fariszuh/12s-EV-Battery-Management-System/Referensi Desain Sebelumnya/BMS Winconsing Racing/218e_battery_design_board_tkhiNwzb7J.pdf

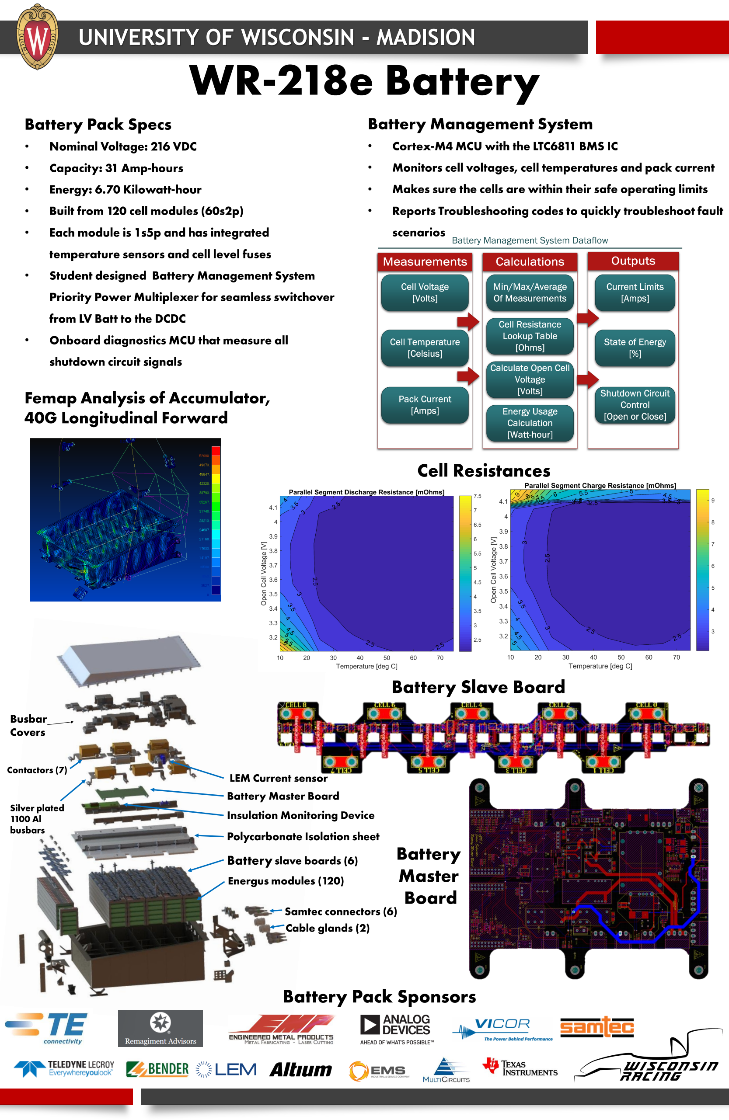
[picture p90: page 1]

UNIVERSITY OF WISCONSIN - MADISION

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
