fariszuh/12s-EV-Battery-Management-System/Referensi Desain Sebelumnya/BMS Orion/wiring overview.png

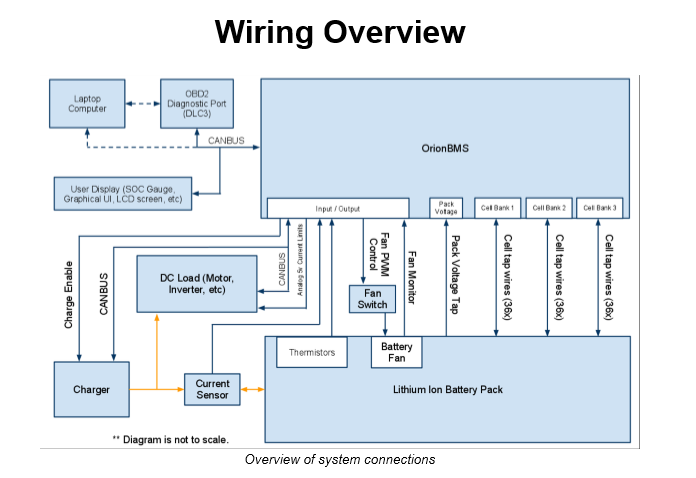
Referensi Desain Sebelumnya/BMS Orion/wiring overview.png
