fariszuh/12s-EV-Battery-Management-System/Adapter IC/Gerber/print.pdf

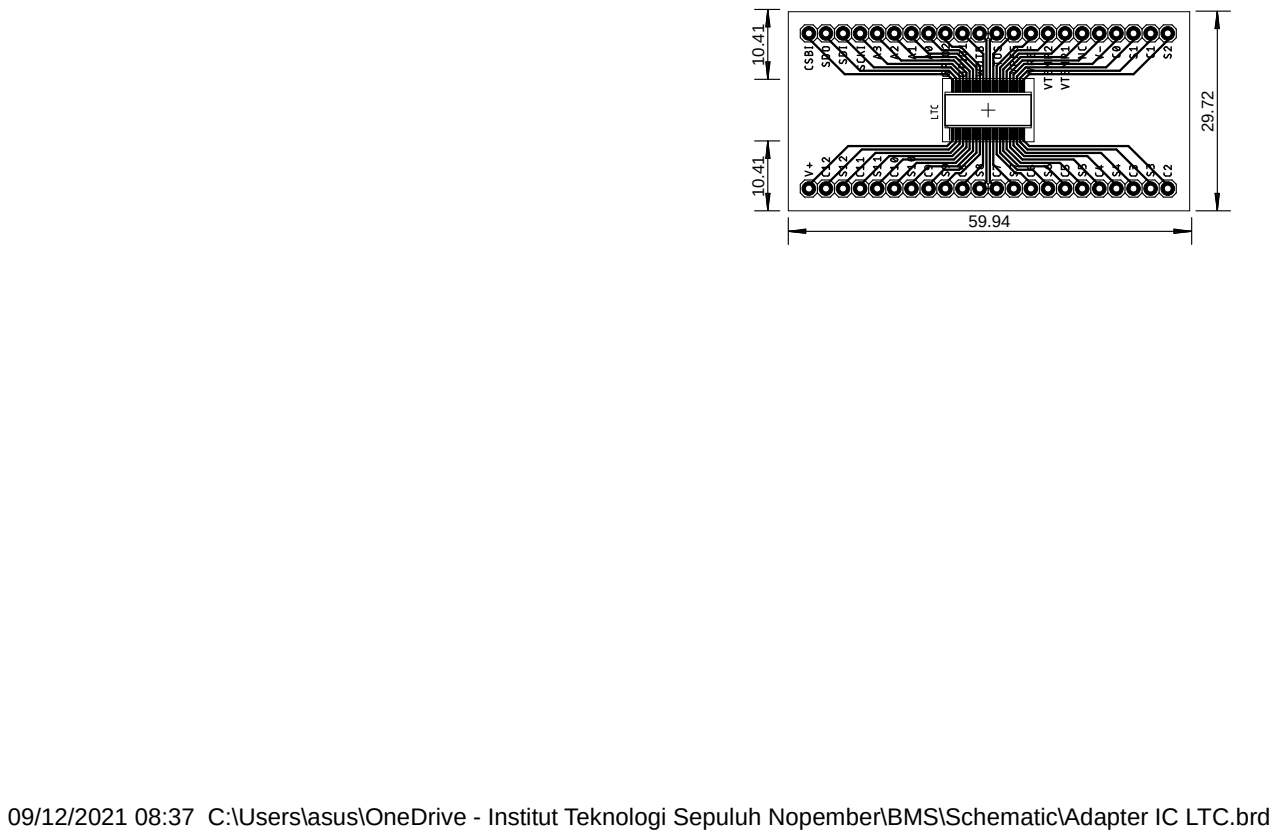
[picture p105: page 1]

09/12/2021 08:37 C:\Users\asus\OneDrive - Institut Teknologi Sepuluh Nopember\BMS\Schematic\Adapter IC LTC.brd

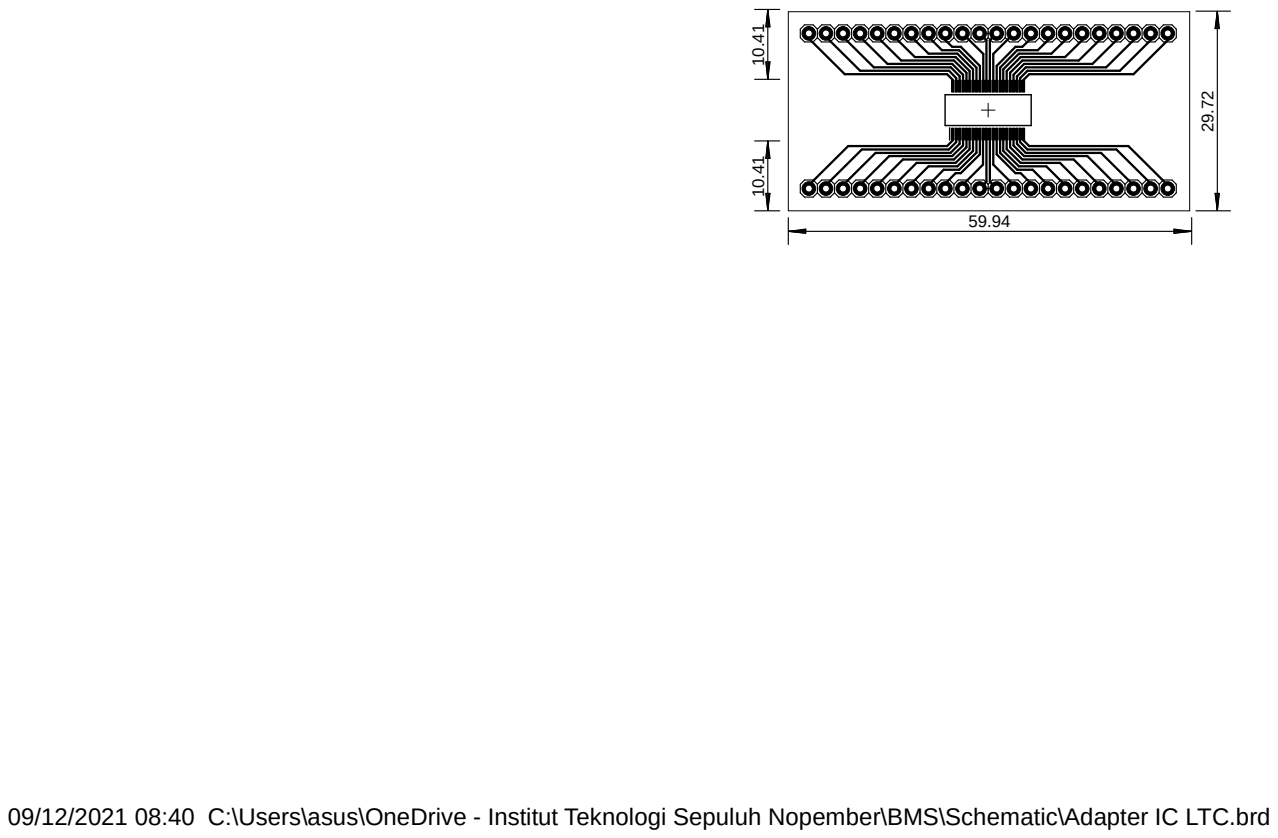
[picture p106: page 2]

09/12/2021 08:40 C:\Users\asus\OneDrive - Institut Teknologi Sepuluh Nopember\BMS\Schematic\Adapter IC LTC.brd
