fariszuh/12s-EV-Battery-Management-System/Referensi Desain Sebelumnya/BMS Winconsing Racing/battery_master_board_6TADGDZ8Km.pdf

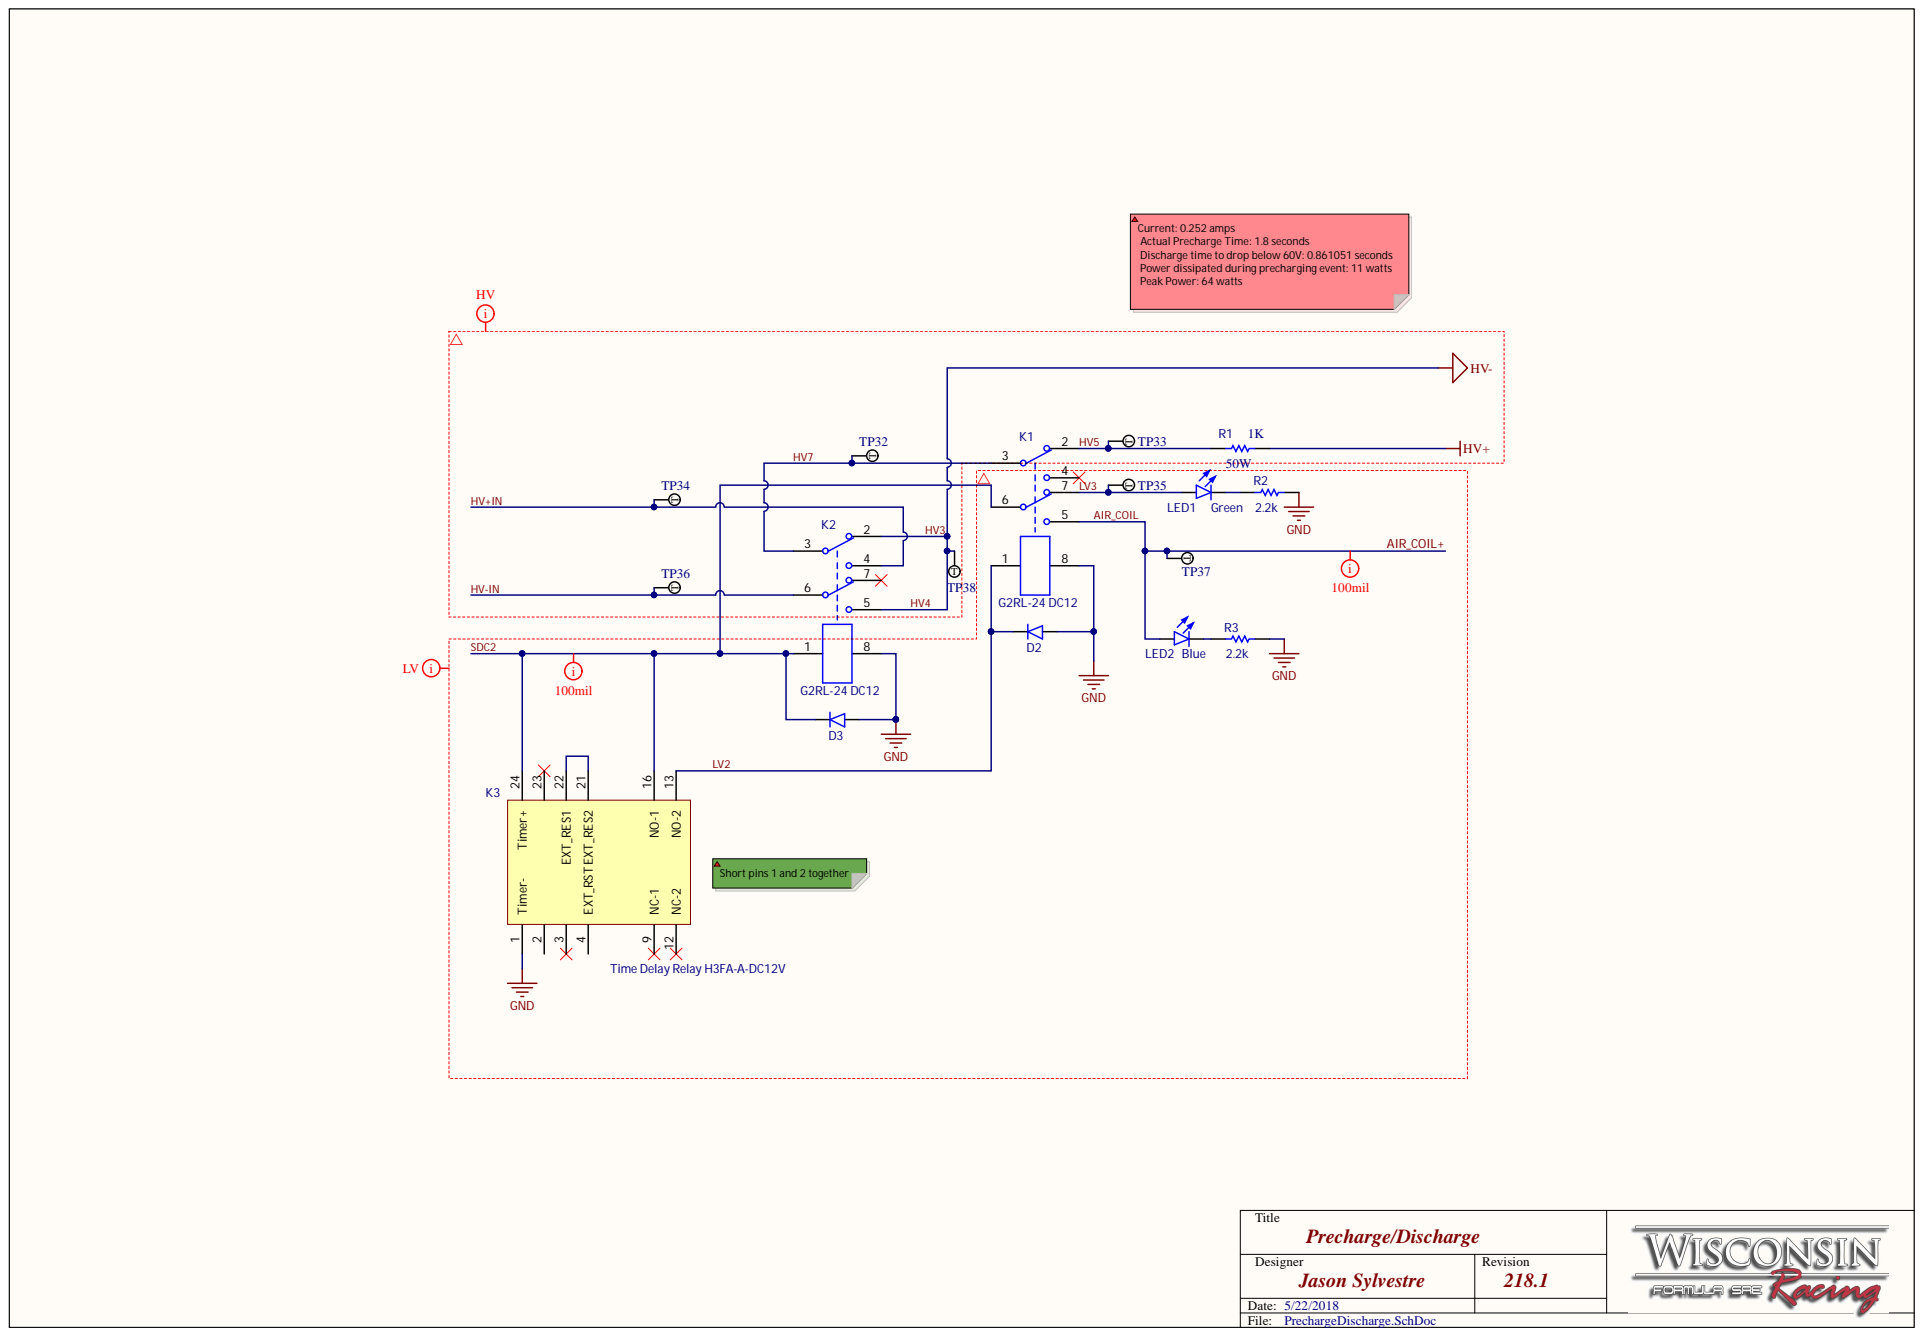
[picture p107: page 1]

Current: 0.252 amps
Actual Precharge Time: 1.8 seconds
Discharge time to drop below 60V: 0.861051 seconds
Power dissipated during precharging event: 11 watts
Peak Power: 64 watts

AIR_COIL

K2 2
3 4

Short pins 1 and 2 together

Title Precharge/Discharge

Designer Jason Sylvestre | Revision 218.1

Date:

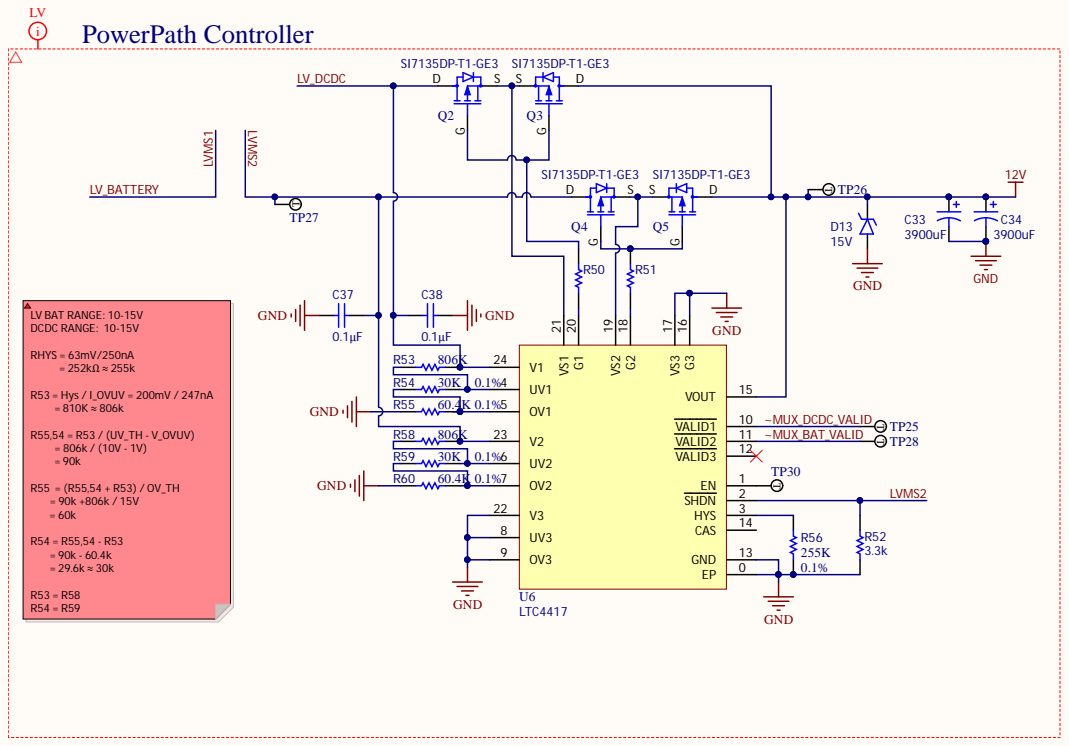
[picture p108: page 2]

R54 30K | 0.1% | UV1 4
R55 60.4K 0.1% | | OV1 5

R58 806K | | V2 23
R59 30K | 0.1% | UV2 6
R60 60.4K 0.1% | | OV2 7

Title Powerpath

Designer Jason Sylvestre | Revision 218.1

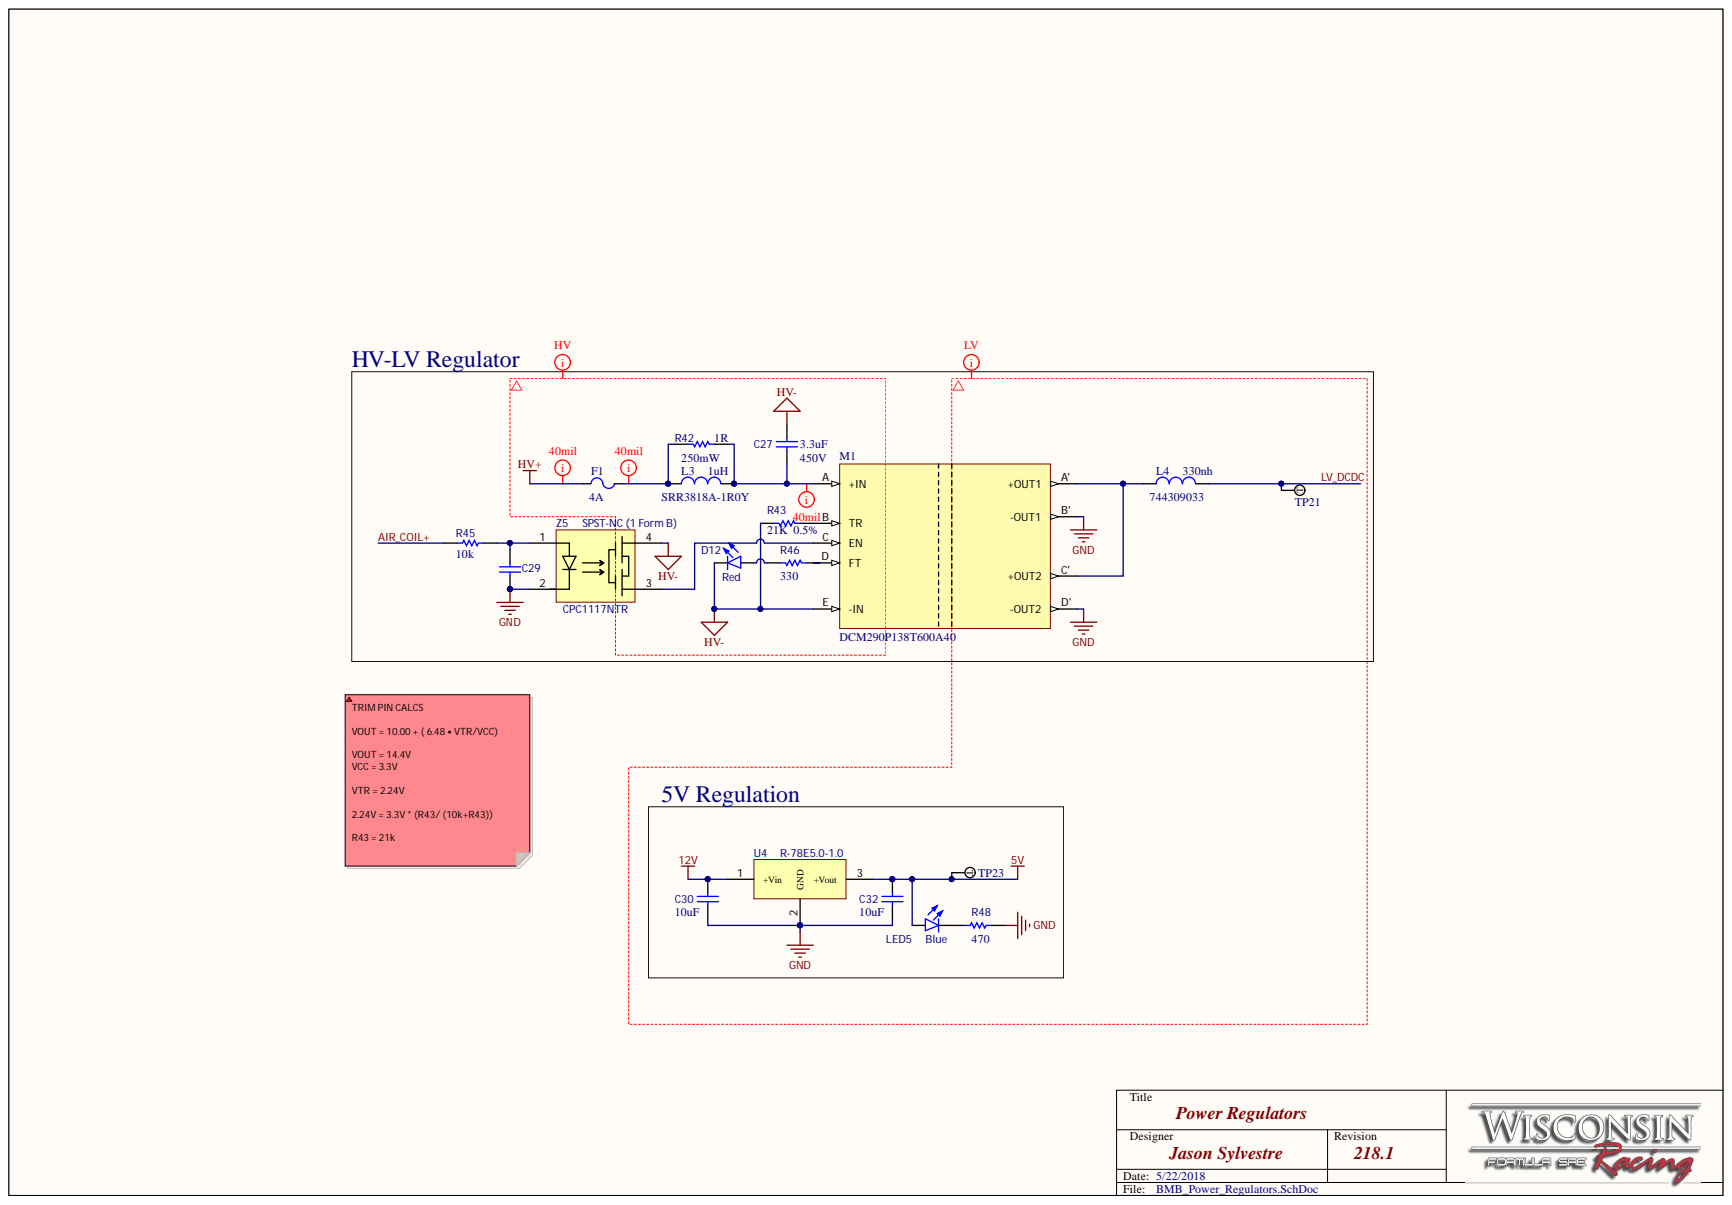
[picture p109: page 3]

Red | 330 | -IN E

Title Power Regulators

Designer Jason Sylvestre | Revision 218.1

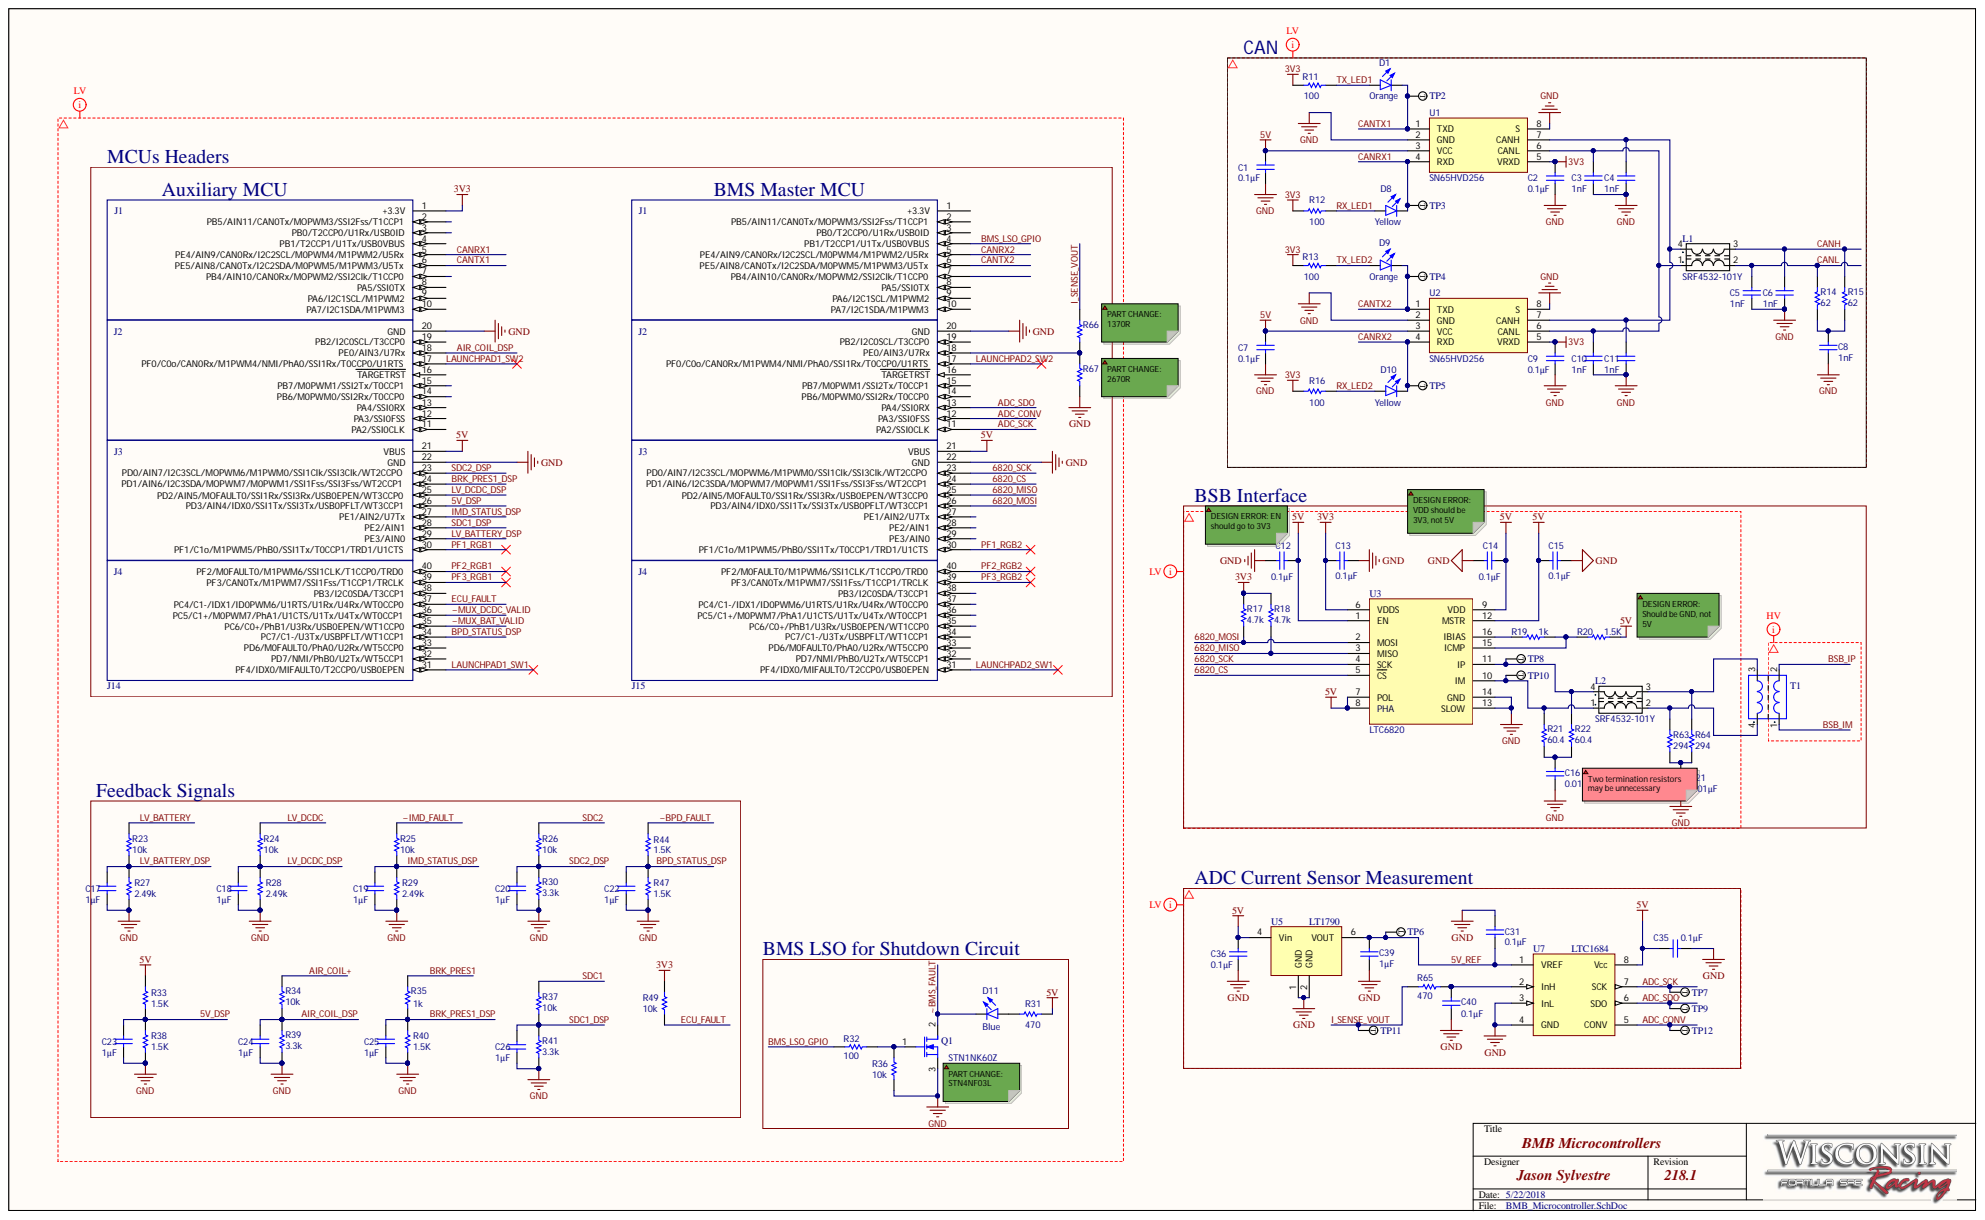
[picture p110: page 4]

ADC Current Sensor Measurement

BMS LSO for Shutdown Circuit

Title BMB Microcontrollers

Designer Jason Sylvestre | Revision 218.1

Date: 5/22/2018

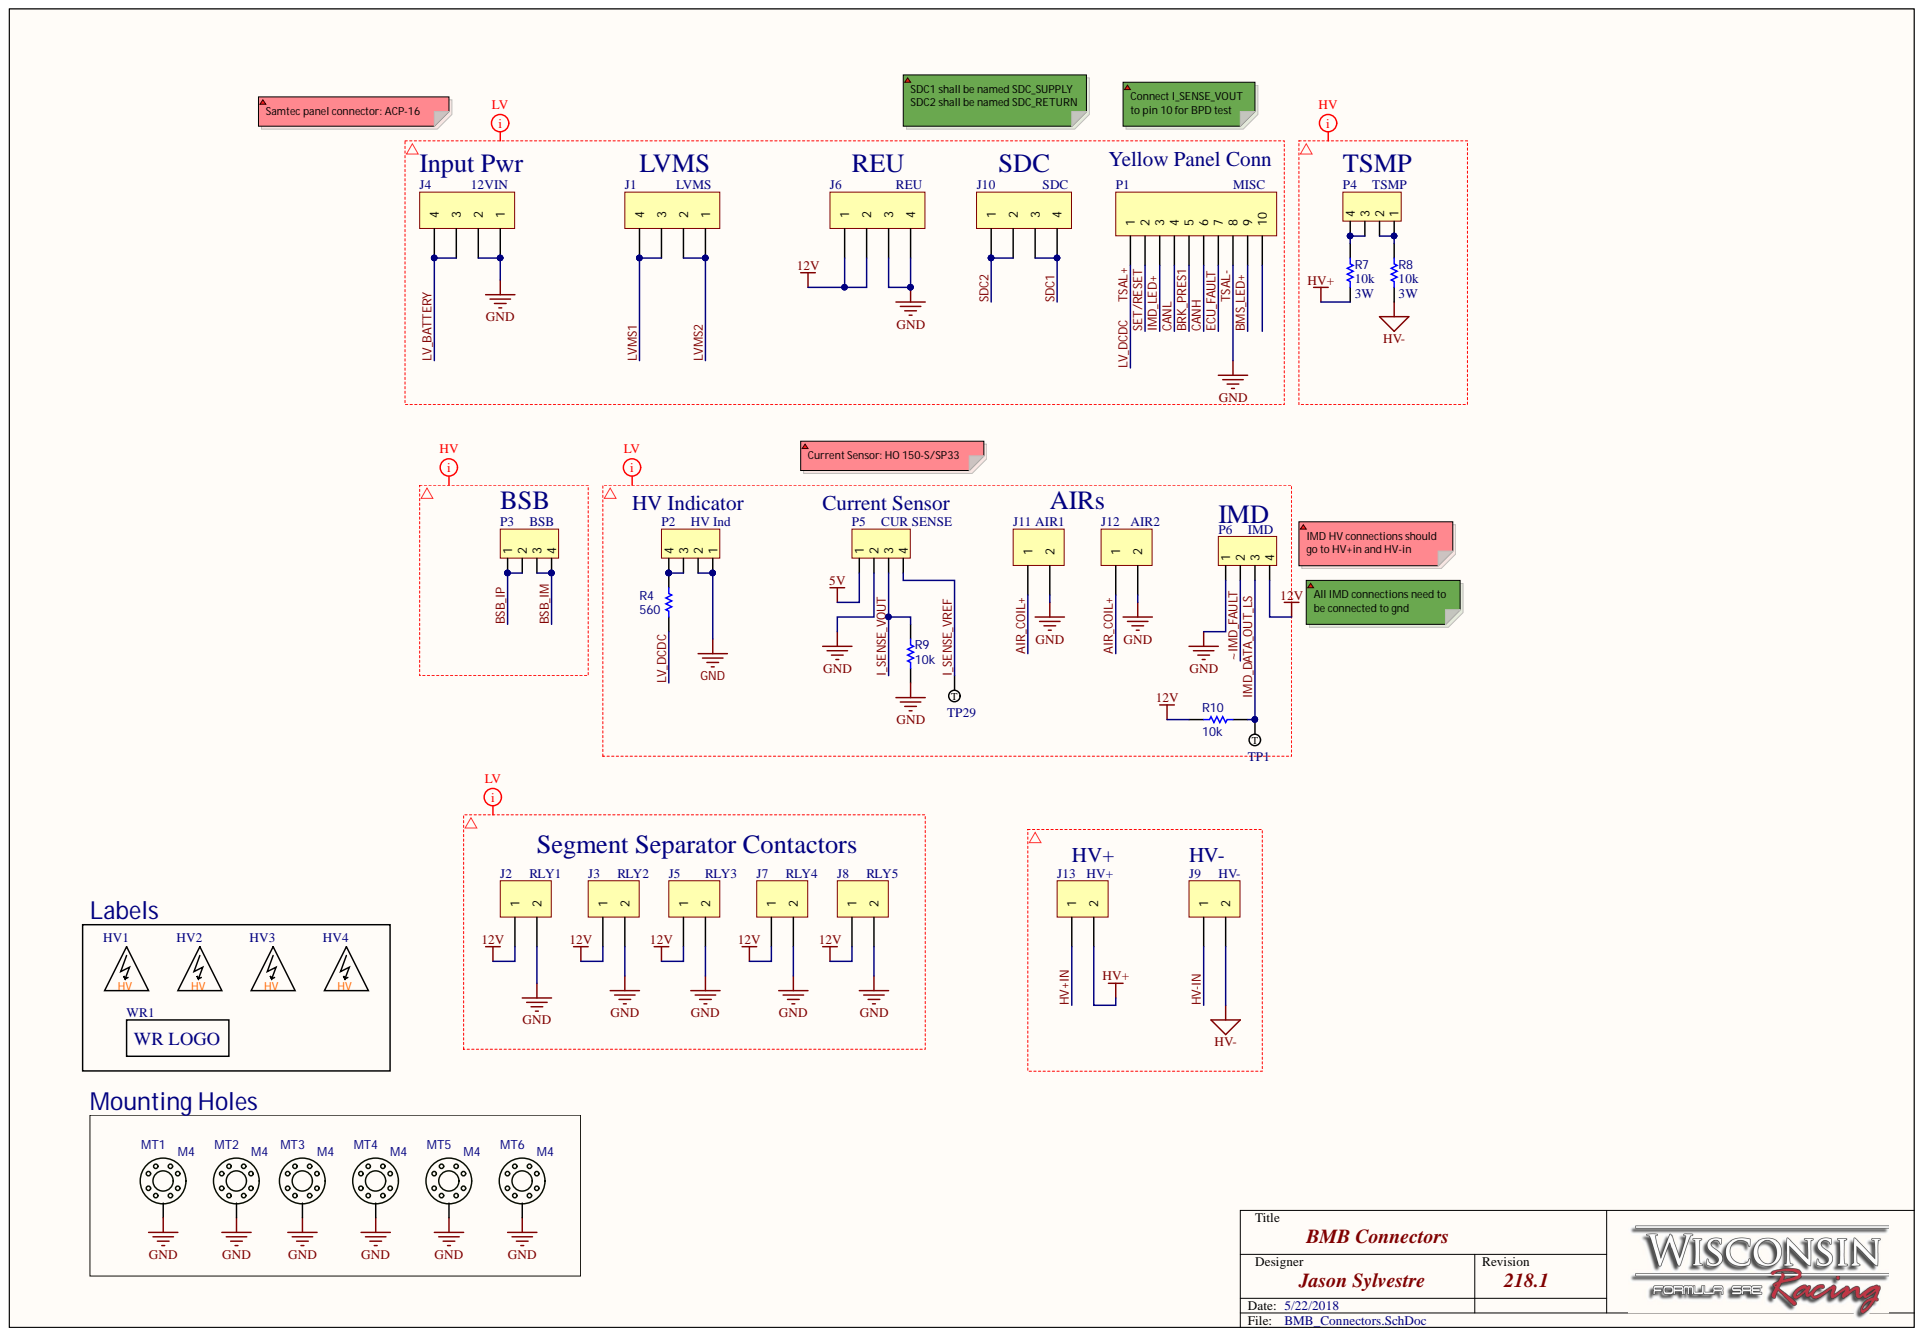
[picture p111: page 5]

Samtec panel connector: ACP-16

Connect I_SENSE_VOUT
to pin 10 for BPD test

IMD HV connections should
go to HV+in and HV-in

All IMD connections need to

be connected to gnd

Title BMB Connectors

Designer Jason Sylvestre | Revision 218.1

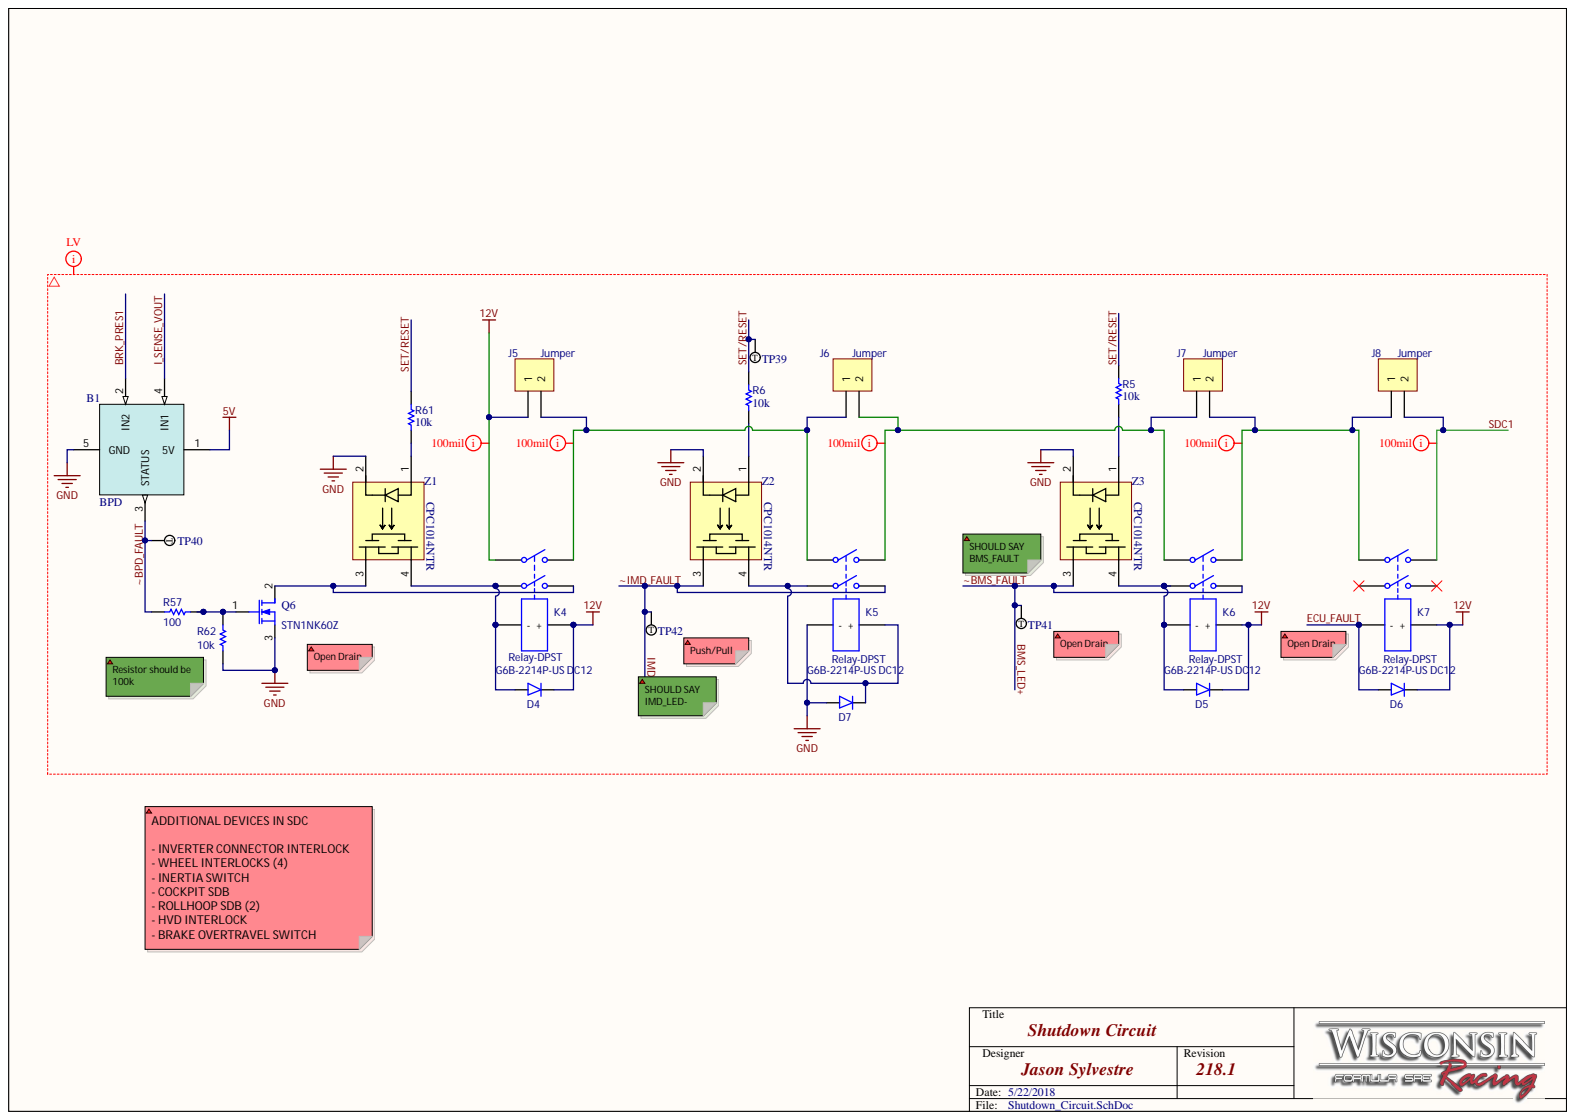
[picture p112: page 6]

ADDITIONAL DEVICES IN SDC

Title Shutdown Circuit

Desig ner Jason Sylvestre | Revisio n 218.1

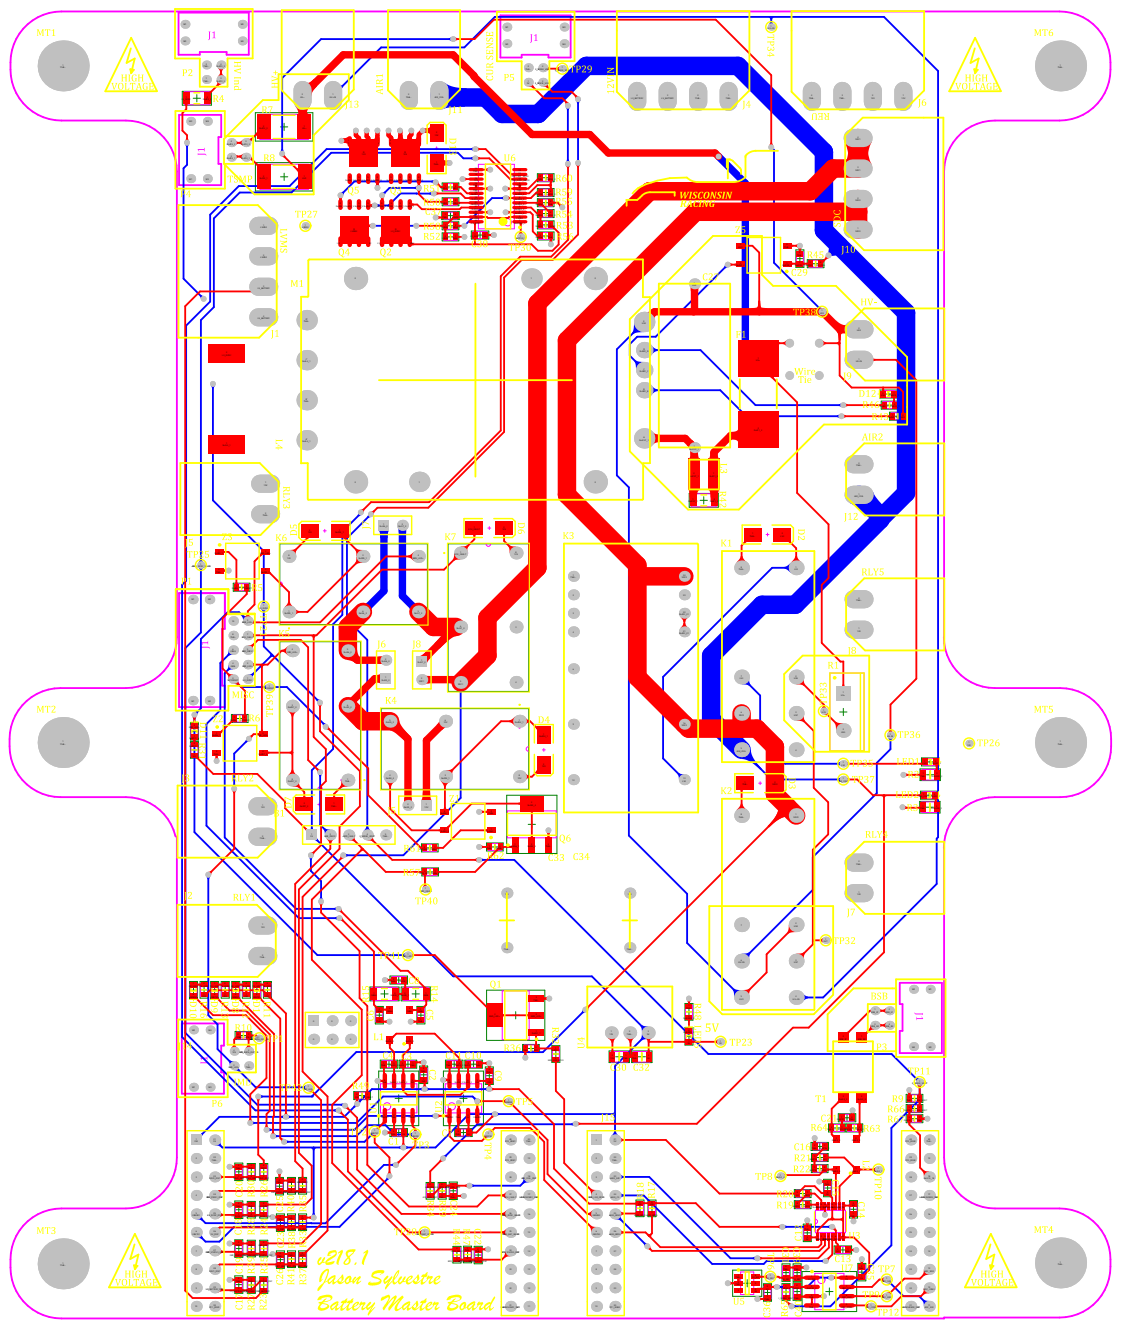
[picture p113: page 7]

NetF1_2 2 | | NetM1_B 1 | HV3 2

NetM1_D 1 NetD12_1 2

NetJ5_2 NetJ5_2 1 1 | SDC1

1 | 2 1 2 1 2 1 | 2 1 TSAL-NetC8_1

TSAL- | ADC_CONV
