fariszuh/12s-EV-Battery-Management-System/Referensi Desain Sebelumnya/BMS Winconsing Racing/bsb_Y9IdNkuxfA.pdf

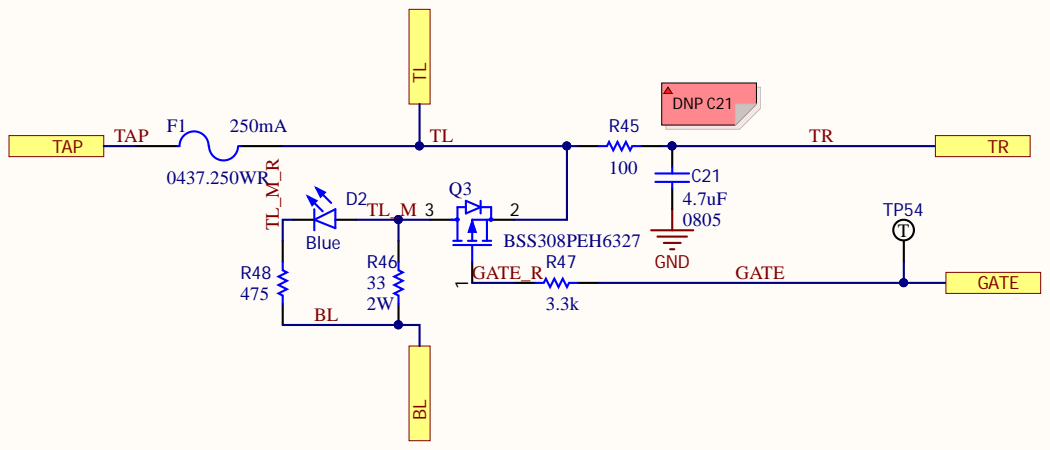
[picture p114: page 1]

Title Balance Circuitry

Designer Jason Sylvestre | Revision 218.1

Date: 5/22/2018

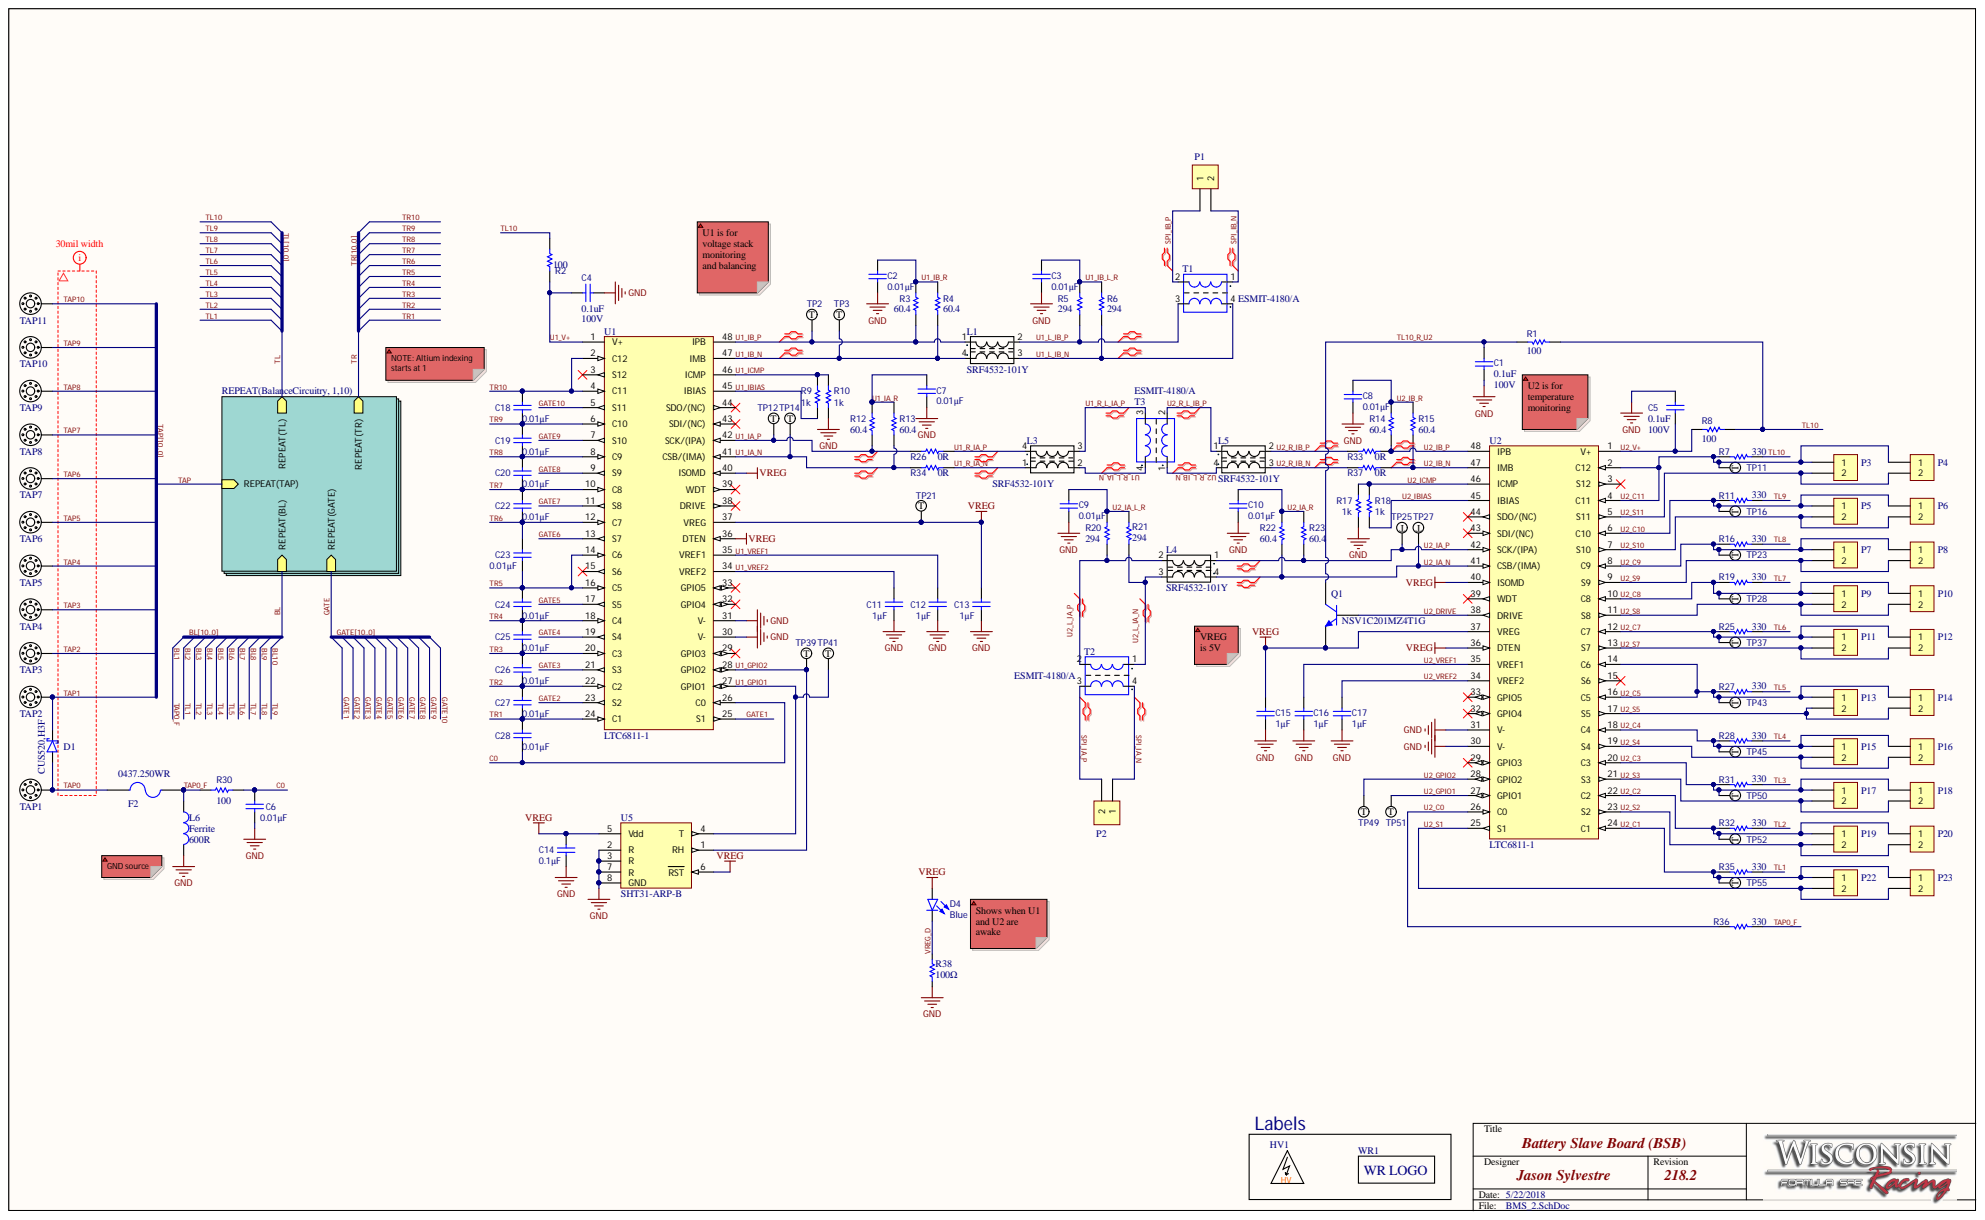
[picture p115: page 2]

C12 2 | U1_IB_N | | 4 | 3 U1_L_IB_N
S12 3 | U1_ICMP SRF4532-101Y

REPEAT(TL) REPEAT(BL)

R 3 | VREG

Title
Battery Slave Board (BSB)

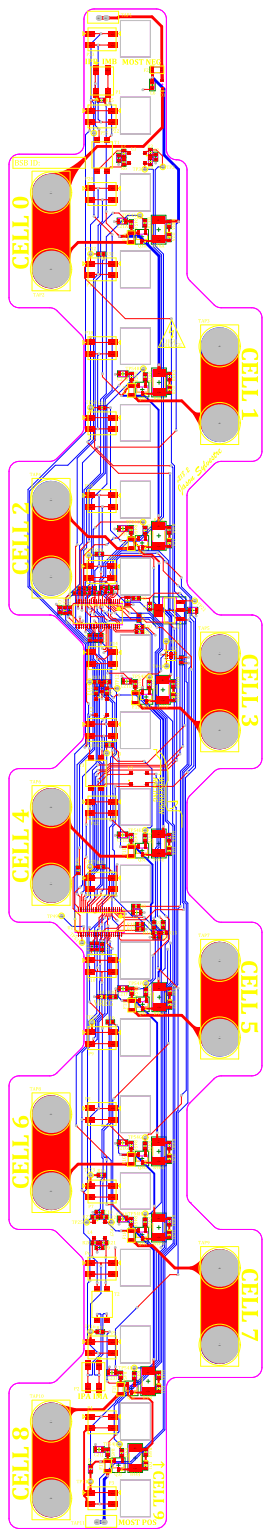
[picture p116: page 3]

GATE3 GATE3 1 1 GND 2 TR3 1 GATE3 | TL_MC 1

U2_V+ 2 GND 1 U2_IBIAS 2

2 1 1 1 2 GND TR9 GATE9 1 | BL9 2 1
