fariszuh/12s-EV-Battery-Management-System/Single Board 12s/Gerber Cetak PENS/bottom.pdf

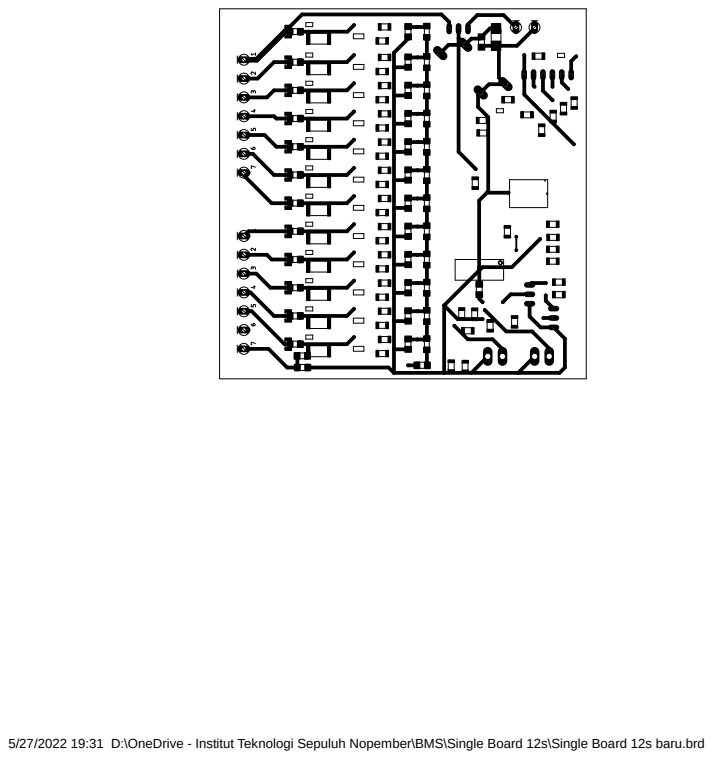
[picture p117: page 1]

5/27/2022 19:31 D:\OneDrive - Institut Teknologi Sepuluh Nopember\BMS\Single Board 12s\Single Board 12s baru.brd
