fariszuh/12s-EV-Battery-Management-System/Single Board 12s/Gerber Cetak PENS/top-LAPTOP-LV46M3MI.pdf

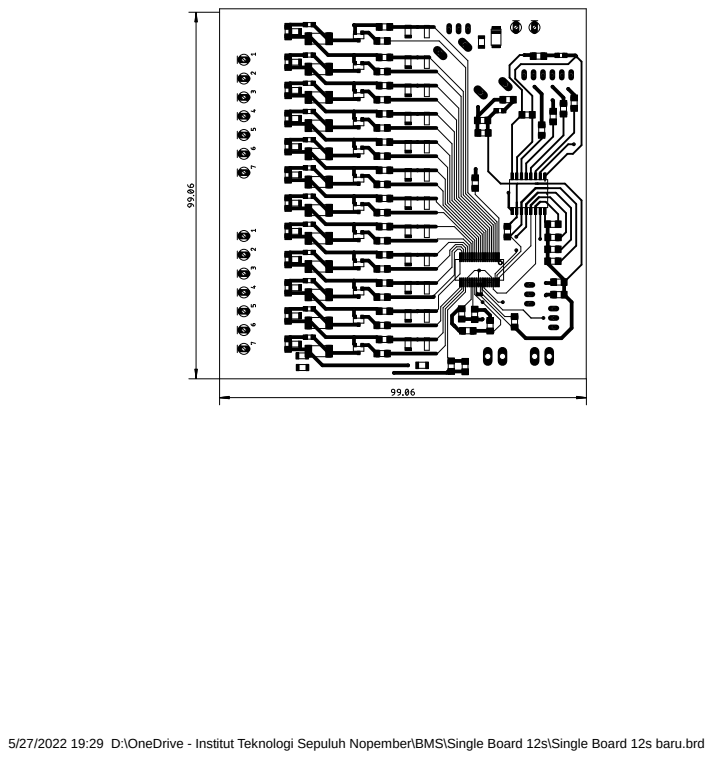
[picture p118: page 1]

5/27/2022 19:29 D:\OneDrive - Institut Teknologi Sepuluh Nopember\BMS\Single Board 12s\Single Board 12s baru.brd
