fariszuh/12s-EV-Battery-Management-System/Adapter IC/Gerber/print no marking.pdf

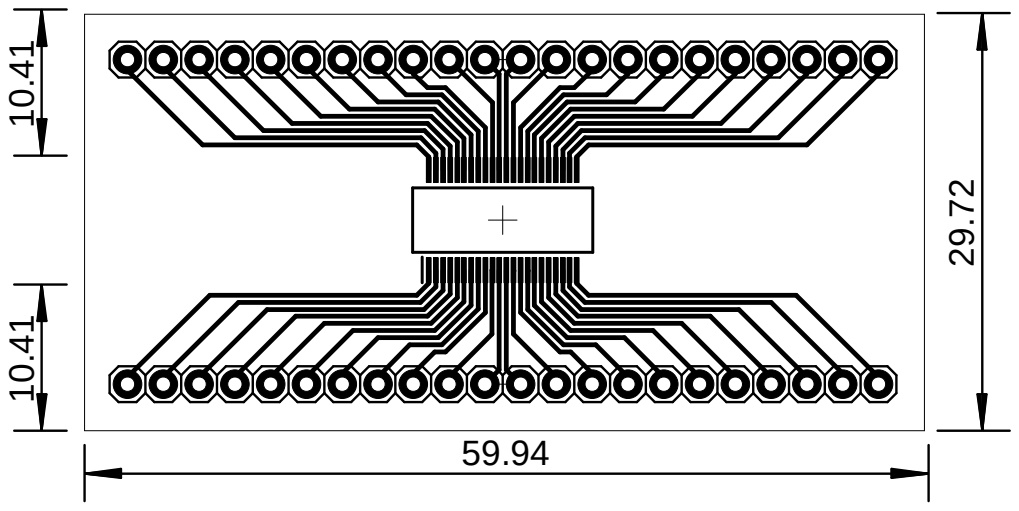
[picture p119: page 1]
